orodamaral/drumcore/docs/00-visao-geral.md

# Visão Geral do Projeto

## Objetivo

Desenvolver um módulo MIDI-USB para bateria eletrônica, usando ESP32-S3 como
cérebro do sistema, capaz de:

1. Ler até 32 entradas analógicas (pads piezo simples/aro, pratos 2/3 zonas,
   chimbal simples/2 zonas, pedal de chimbal FSR/óptico) através de 2
   multiplexadores CD4067 (módulo breakout "HW-178", 16 canais cada) — o
   tipo de cada canal é configurável pelo app, ver
   [05-tipos-de-sensor.md](05-tipos-de-sensor.md).
2. Converter os sinais lidos em eventos MIDI (Note On/Off, Control Change) e
   enviá-los via **USB-MIDI nativo** (classe de dispositivo USB, plug-and-play,
   sem necessidade de driver ou software intermediário como Hairless MIDI) e
   também via **BLE-MIDI** (Bluetooth, simultâneo ao USB) — ver
   [01-decisoes-arquiteturais.md](01-decisoes-arquiteturais.md).
3. Prever uma tela (TFT ST7735 1.8" 128x160, SPI, paisagem) e 1 encoder
   rotativo com chave (girar navega/ajusta valor, clicar desce um
   nível/confirma, segurar volta um nível — Fase Y) para configuração do
   módulo diretamente no hardware (sensibilidade, threshold, curva, nota
   MIDI de cada pad, etc).
4. Oferecer um app de configuração, direto pelo navegador (Web Serial), para
   ajustar todos os parâmetros de cada pad, mapeamento de notas e
   backup/restore de configuração.

## Escopo funcional (alto nível)

| # | Funcionalidade | Status |
|---|---|---|
| 1a | Leitura de 32 canais via 2x CD4067/HW-178 (sensing) | Compilado, sem teste em hardware real |
| 1b | Envio MIDI-USB nativo (Note On/Off) | Compilado, sem teste em hardware real |
| 1c | Envio BLE-MIDI simultâneo ao USB (Bluetooth) | Compilado, sem teste em hardware real |
| 2 | Tela TFT (ST7735) + 1 encoder rotativo de configuração (rotate/click/hold, Fase Y) | Compilado, sem teste em hardware real |
| 2b | Persistência EEPROM (config por pad sobrevive a reboot) | Compilado, sem teste em hardware real |
| 2c | Protocolo serial NDJSON (módulo ↔ app) | Compilado, sem teste em hardware real |
| 2d | Nome livre por pad (editável só pelo app) | Compilado/build ok, sem teste em hardware real |
| 2e | 9 tipos de sensor por pad + topologia de canais configurável pelo app | Compilado/build ok, sem teste em hardware real |
| 2f | Navegação de 6 telas (BOOT/LIVE/PADS/PAD_EDIT/SIGNAL/GLOBAL, design/SPEC.md) — substitui a tela/grid da Fase I | Compilado/build ok, sem teste em hardware real |
| 2g | Canal habilitado/desabilitado por pad (evita ruído em slot sem sensor) | Compilado/build ok, sem teste em hardware real |
| 3 | App de configuração (Web Serial, direto pelo navegador), visual unificado com o site | Build/typecheck ok, sem teste com módulo real (só modo demo) |

Projeto renomeado de "HelloDrum" para "DrumCore" em 2026-08-21 (ver
[01-decisoes-arquiteturais.md](01-decisoes-arquiteturais.md), Fase J) — a
biblioteca de terceiros vendorizada mantém o nome original.

## Decisões já tomadas

Ver [01-decisoes-arquiteturais.md](01-decisoes-arquiteturais.md) para o histórico
completo e o racional de cada decisão. Resumo:

- **Placa**: ESP32-S3 (USB OTG nativo → permite USB-MIDI classe de dispositivo).
- **Toolchain**: PlatformIO.
- **Biblioteca base**: [HelloDrum-arduino-Library](https://github.com/RyoKosaka/HelloDrum-arduino-Library),
  vendorizada (fork local) em `firmware/lib/HelloDrum-arduino-Library`, para podermos
  modificar livremente.

## Como este projeto é documentado

- **docs/01-decisoes-arquiteturais.md** — registro de decisões técnicas (estilo ADR),
  com contexto e alternativas consideradas.
- **docs/02-hardware.md** — esquema de ligação (pinout ESP32-S3 ↔ 2x CD4067
  (HW-178) ↔ pads, tela TFT, encoder).
- **docs/03-biblioteca-hellodrum.md** — notas sobre a API da biblioteca base, o que
  foi entendido do código-fonte, e o que foi/será modificado em relação ao original.
- **docs/04-protocolo-serial.md** — contrato de comunicação (NDJSON) entre o
  firmware e o app.
- **docs/05-tipos-de-sensor.md** — os 9 tipos de sensor suportados, quantos
  canais cada um usa, e como o link pedal↔chimbal funciona.
- **docs/06-edicao-arduino.md** — ideia (não implementada) de uma edição para
  Arduino Mega/Uno, incluindo uma versão lite com 16 canais diretos.
- **docs/07-estudo-prato-3-zonas.md** — estudo de como os módulos comerciais
  leem um ride de 3 zonas, e o caminho escolhido (prato de 2 piezos).
- **docs/CHANGELOG.md** — o que foi feito, em ordem cronológica.

Sempre que uma decisão relevante for tomada ou algo novo for aprendido sobre a
biblioteca/hardware, isso deve ser registrado nesses arquivos.
