orodamaral/drumcore/design/DrumCore Logos.dc.html

TURNO 1 · 5 DIREÇÕES

DrumCore — marcas

Marcas tipográficas e geométricas, construídas na mesma paleta da UI. Cada opção mostra a versão grande, a versão 1-bit (para a tela de boot em 128 px) e o ícone quadrado.

1A Pixel · grade de pads

DRUMCORE

DRUMCORE

1-BIT 128PX

ÍCONE

1B Peso partido · sans

DRUMCORE

DRUMCORE

1-BIT 128PX

DC

ÍCONE

1C Núcleo concêntrico · lockup

DRUMCORE

TRIGGER MODULE

DRUMCORE

1-BIT 128PX

ÍCONE

1D Envelope · linha de base

DRUMCORE

DRUMCORE

1-BIT 128PX

ÍCONE

1E Placa · monograma em caixa

DC

DRUMCORE 32 PAD · ESP32-S3

DC

DRUMCORE

1-BIT 128PX

DC

ÍCONE

NA TELA DE BOOT

DRUMCORE

v0.1 ESP32-S3

{{ b.id }} · 128PX @2X
