orodamaral/drumcore/design/Modulo Bateria UI.dc.html

⚠ Desatualizado (Fase Y, 2026-09-04): este mockup ainda mostra a navegação de 2 encoders (ENC1/ENC2). O firmware real usa 1 encoder só (rotate/click/hold) desde a Fase Y — ver design/SPEC.md seção 1-2 pro comportamento atual. Este arquivo não foi reconstruído pro modelo novo.

ESP32-S3 · TFT 1.44" 128x128

Módulo de bateria — UI

Especificação de telas, navegação, tokens e widgets para implementação. Todas as telas são desenhadas em pixels reais de 128x128 e mostradas ampliadas para leitura.

Controles2 rotary encoders c/ botão

Pads32 · grade 8x4

01 — CONTROLES

ENC 1 — página

{{ r.k }} {{ r.v }}

ENC 2 — navegação e valor

{{ r.k }} {{ r.v }}

02 — TELAS

DRUMCORE

32 PAD TRIGGER

v0.1 ESP32-S3

SCR 0 Boot

Exibida durante init de I2S/ADC e leitura da EEPROM. Barra reflete progresso real do boot. Sai automaticamente para LIVE ao terminar; qualquer botão pula a espera.

DRUMCORE

32 PAD TRIGGER

v0.1 ESP32-S3

TAMANHO
REAL

LIVE USBDIN

{{ p.n }}

SCR 1 Live

Tela padrão. Ao receber trigger, o pad acende sólido em laranja por 60 ms e decai em 2 passos (borda laranja, depois idle) em ~180 ms. Nunca redesenhar a grade inteira: só o retângulo do pad.

{{ s.label }}

LIVE USBDIN

{{ p.n }}

TAMANHO
REAL

PADS07/32

{{ r.t }} {{ r.sens }} {{ r.note }}

SCR 2 Lista de pads

8 linhas de 14 px visíveis, janela deslizante sobre os 32 pads. A seleção só rola quando encosta na 1ª ou 8ª linha. Colunas: índice, sensor abreviado, nota MIDI. ENC2 push abre a edição do pad selecionado.

PADS07/32

{{ r.t }} {{ r.sens }} {{ r.note }}

TAMANHO
REAL

PAD 07EDIT

{{ r.k }} {{ r.v }}

ENC2 GIRA VALORPUSH OK

SCR 3 Edição do pad

Os 7 parâmetros cabem sem rolagem (7 × 14 px). Linha selecionada em ciano; ao entrar em modo edição o valor vira caixa âmbar e o giro do ENC2 passa a alterar o número. ENC1 troca de pad sem sair da tela.

{{ p.k }}{{ p.r }}

PAD 07EDIT

{{ r.k }} {{ r.v }}

ENC2 GIRA VALORPUSH OK

TAMANHO
REAL

PAD 07SIGNAL

VEL104PEAK118

SCAN 2MASK 30THR 12

SCR 4 Monitor de sinal

Último envelope capturado do pad (buffer de 120 amostras, 1 px por amostra). Faixa ciano = janela de scan, faixa cinza = mask time, linha âmbar = threshold. Redesenha só quando chega um hit novo, não em loop.

PAD 07SIGNAL

VEL104PEAK118

SCAN 2MASK 30THR 12

TAMANHO
REAL

GLOBAL

{{ r.k }}{{ r.v }}

SALVO 32 PADS EM NVS

SCR 5 Menu global + toast

Ajustes do módulo e ações de persistência. O toast é um overlay de 100×34 px centrado, exibido por 900 ms e depois apagado restaurando a área por baixo. Sem confirmação modal: salvar é ação direta.

GLOBAL

{{ r.k }}{{ r.v }}

SALVO 32 PADS EM NVS

TAMANHO
REAL

03 — MAPA DE NAVEGAÇÃO

BOOT

──▶ init concluído

ENC1 GIRA

{{ p.n }}

◀▶

volta ao início (circular)

ENC2 PUSH

{{ t.from }} {{ t.ev }} ▶ {{ t.to }}

04 — TOKENS

NOME HEX RGB565 USO {{ t.name }} {{ t.hex }} {{ t.r565 }} {{ t.use }}

TIPOGRAFIA

{{ t.k }}{{ t.v }}

MÉTRICA

{{ t.k }}{{ t.v }}

05 — WIDGETS

{{ w.name }} {{ w.size }}

{{ w.desc }}

·{{ r }}
