orodamaral/drumcore/site/assets/schematic.html

DrumCore · Módulo MIDI-USB

# Esquemático de ligação — ESP32-S3

ESP32-S3 ↔ 1 encoder rotativo com chave + tela TFT ST7735 (SPI) de um lado ↔ 2x multiplexador CD4067/HW-178 (32 canais de pad) do outro. Pinout conforme firmware/src/main.cpp (https://github.com/orodamaral/drumcore/blob/master/firmware/src/main.cpp) e docs/02-hardware.md (https://github.com/orodamaral/drumcore/blob/master/docs/02-hardware.md).

Tudo validado em hardware real: encoder + tela (2026-09-06) e as 2 jackboards com MUX (2026-10)

Seleção/leitura dos CD4067/HW-178 (S0–S3, SIG)

SPI — tela TFT ST7735

Encoder rotativo (A/B/SW)

Alimentação (anotada em texto, não desenhada como fio)

Fase Z (2026-09-05): a placa ganhou pads de 3V3/GND extras nos dois headers (modificação física, fora do dev board original) — a divisão deixou de ser "quem precisa de VCC" (Fase L) e passou a ser por função: interface do usuário (encoder + tela, 9 sinais contíguos) no header ESQUERDO; sensing (2x CD4067/HW-178, 6 sinais contíguos) no header DIREITO — mesmo bloco de pinos que os 2 encoders usavam antes das Fases Y/Z. SIG0/SIG1 usam os 2 únicos pinos ADC desse bloco (GPIO2 na jackboard A, GPIO1 na B, ambos ADC1, que funciona com o Wi-Fi ligado); S0-S3 usam os 4 pinos digitais restantes (GPIO39–42). Barramento S0/S1/S2/S3 compartilhado entre os 2 módulos; cada placa usa seu próprio pino SIG. Pontos pretos = junção elétrica real.

### Por que a divisão mudou (Fase Z)

Até a Fase Y, 3V3 só existia no header esquerdo, então o MUX e a tela (que precisam de VCC) ficavam à força ali. A placa física ganhou pads de 3V3/GND extras nos dois headers — isso libera a divisão pra seguir uma lógica de FUNÇÃO em vez de alimentação: encoder + tela (interface) de um lado, MUX (sensing) do outro. Ver docs/01-decisoes-arquiteturais.md (https://github.com/orodamaral/drumcore/blob/master/docs/01-decisoes-arquiteturais.md) (Fase Z).

### MUX: ADC1 em vez de ADC2

O bloco contíguo do header direito (1,2,42,41,40,39) só tem 2 pinos com ADC: GPIO1/GPIO2 (ADC1_CH0/CH1) — por isso SIG0/SIG1 ficam neles, e S0-S3 (sem precisar de ADC) ficam nos outros 4. Antes (Fase L) o MUX usava ADC2 (GPIO15/16), que exigia justificar que não haveria conflito com Wi-Fi. Em ADC1 esse cuidado nem precisa existir.

### Tela: espelhada com o conector de novo (2026-09-06)

Na Fase Z, a tela passou a seguir só a contiguidade com o encoder, sem se preocupar em casar com a ordem do conector dela. A pedido do Rodrigo, isso mudou de novo: dentro do bloco fixo 7,15,16,17,18,8 (a posição do bloco não mudou), os 6 sinais foram reordenados pra bater com a sequência física do conector da tela (GND VDD SCL SDA RES DC CS BLK) — SCL(7) → SDA(15) → RES(16) → DC(17) → CS(18) → BLK(8). GND/VDD da tela vão em pads extras perto desse bloco (não existe 3V3/GND de fábrica bem ali).

### Pinos evitados

- Strapping pins (GPIO0, 3, 45, 46)
- Pinos do USB nativo (GPIO19/20 — usados pelo USB-MIDI)
- GPIO38 — aciona um LED embutido (BUILTIN LED) dessa placa específica
- GPIO47/48 — internos de flash/PSRAM nessa placa; GPIO48 também é o LED RGB endereçável (RGB LED)
- GPIO43/44 — não estão livres: são o UART físico usado pelo Serial (protocolo NDJSON)

### HW-178 (CD4067) — pino EN fixo em GND

O breakout expõe um pino EN (enable, ativo em LOW) que a lib não controla — decisão de fiação, não de firmware: ligado direto em GND nas 2 placas, sempre habilitadas. Como cada MUX tem seu próprio pino SIG, não há necessidade de desabilitar um deles em nenhum momento.

### Encoder — sem resistor externo

A/B/SW usam INPUT_PULLUP interno do ESP32-S3 (ver firmware/src/main.cpp (https://github.com/orodamaral/drumcore/blob/master/firmware/src/main.cpp)) — não precisa de resistor de pull-up na placa. O módulo físico que chegou também tem pull-ups próprios (VCC no 3V3) — os dois ativos ao mesmo tempo não causam problema elétrico.

### Histórico de ajustes de pinout

2026-08-31: contiguidade dentro de cada header. Fase Y (2026-09-04): 2 encoders → 1 só, o que sobrou ficou em GPIO41/40/39 (GPIO1/2/42 livres). Fase Z (2026-09-05): encoder + tela migraram pro header esquerdo (mesmo bloco contíguo 4,5,6,7,15,16,17,18,8); o MUX migrou pro header direito (bloco 1,2,42,41,40,39, o mesmo que os 2 encoders usavam antes). 2026-10-01: ajustado na montagem da jackboard A — S0–S3 = GPIO39/40/41/42 (ordem invertida) e os SIGs trocaram (A = GPIO2, B = GPIO1).

### O que já foi validado, o que ainda não

Validado (2026-09-06): encoder (GPIO4/5/6, navegação girar/clicar/segurar confirmada) e tela (GPIO7/15/16/17/18/8, imagem confirmada). Validado (2026-10): as 2 jackboards montadas com os CD4067 — os 32 canais lidos pelo MUX, com pads de piezo, caixa 3 zonas e o controlador de chimbal (sensor Hall SS49E) no jack 1.

## Referência de pinout

Encoder rotativo — header esquerdo

Sinal | GPIO
A | 4
B | 5
SW (click/hold) | 6

Tela TFT ST7735 — header esquerdo

Sinal | GPIO
SCL (SCK) | 7
SDA (MOSI) | 15
RES | 16
DC | 17
CS | 18
BLK | 8

2x CD4067/HW-178 (32 canais) — header direito

Sinal | GPIO
S0 (compartilhado) | 39
S1 (compartilhado) | 40
S2 (compartilhado) | 41
S3 (compartilhado) | 42
SIG — jackboard A (pads 0–15) | 2
SIG — jackboard B (pads 16–31) | 1

Projeto DrumCore — módulo MIDI-USB para bateria eletrônica. Ver docs/02-hardware.md (https://github.com/orodamaral/drumcore/blob/master/docs/02-hardware.md), docs/01-decisoes-arquiteturais.md (https://github.com/orodamaral/drumcore/blob/master/docs/01-decisoes-arquiteturais.md) e docs/05-tipos-de-sensor.md (https://github.com/orodamaral/drumcore/blob/master/docs/05-tipos-de-sensor.md) no repositório para o racional completo de cada decisão. Licenciado sob CC BY-NC 4.0 (https://github.com/orodamaral/drumcore/blob/master/LICENSE) — uso e cópia livres, sem fins comerciais, sempre citando a fonte.
