orodamaral/drumcore/docs/04-protocolo-serial.md

# Protocolo Serial (módulo ↔ app)

Contrato de comunicação entre o firmware (ESP32-S3, via USB-CDC — a mesma
porta serial já usada pra debug desde a Fase B) e o app de configuração.

## Formato

**NDJSON** (um objeto JSON por linha, terminado em `\n`). Todo o tráfego
Serial usa esse formato — inclusive os eventos de "pad atingido", que antes
eram texto livre (`Serial.print`) e passaram a ser JSON também, pra manter o
stream inteiro consistente e fácil de parsear do lado do app (sem precisar
filtrar linhas de debug misturadas com linhas de protocolo).

Baud rate: 115200 (definido em `firmware/platformio.ini`).

## Canais "primary" vs. canais consumidos

Desde a Fase G (tipos de sensor — ver
[05-tipos-de-sensor.md](05-tipos-de-sensor.md)), nem todo canal (0-31) é um
pad independente: tipos de 2 canais (aro, prato 2/3 zonas, chimbal 2 zonas)
consomem o canal seguinte. Um `pad_config` sempre tem um campo `primary`:

- `"primary": true` — pad independente, com todos os campos de configuração
  (ver tabela abaixo).
- `"primary": false` — canal consumido pelo pad anterior; só tem `pad` e
  `consumed_by` (índice do pad que o está usando). Não aceita `set_pad`
  (retorna `error` com `channel_consumed`).

## Comandos (app → módulo)

Cada linha enviada pelo app é um objeto com um campo `cmd`.

| `cmd` | Campos extras | Descrição |
|---|---|---|
| `ping` | — | Testa a conexão. Resposta: `pong`. |
| `get_device_info` | — | Informações gerais do módulo. Resposta: `device_info`. |
| `get_pad` | `pad` (0-31) | Configuração de um pad. Resposta: `pad_config`. |
| `get_all_pads` | — | Configuração de todos os 32 pads (32 respostas `pad_config` em sequência). |
| `set_pad` | `pad` (0-31), `field`, `value` | Altera um parâmetro de um pad, aplica imediatamente e persiste em EEPROM. Resposta varia por campo (ver tabela) ou `error`. |
| `set_global` | `field`, `value` | Altera uma configuração global (ver tabela abaixo), aplica imediatamente e persiste em EEPROM. Resposta: `ack` + `device_info`. |
| `save_all` | — | Grava toda a configuração atual (32 pads + globais) na EEPROM. Resposta: `log` + `device_info`. Esse comando existe principalmente pro caminho dos encoders/tela (Fase J — ver [01-decisoes-arquiteturais.md](01-decisoes-arquiteturais.md)), onde a edição só fica em RAM até `GLOBAL > SALVAR`; pelo protocolo serial ele é redundante na prática, já que `set_pad`/`set_global` já persistem a cada mudança. |
| `restore_all` | — | Descarta qualquer mudança em RAM e recarrega os 32 pads + globais da EEPROM. Resposta: `pad_config` × 32 + `log` + `device_info`. |
| `factory_reset` | `confirm` (`true`, obrigatório) | Apaga a configuração atual e grava o mapeamento de fábrica (ver [02-hardware.md](02-hardware.md), "Mapeamento de fábrica") em RAM e EEPROM. Sem `"confirm": true` responde `error` `confirm_required`. Resposta: `pad_config` × 32 + `jack_config` × 16 + `log` + `device_info`. |
| `get_timing` | — | Diagnóstico: responde um `log` com o tempo médio e máximo de uma volta do loop (= intervalo entre 2 leituras do mesmo canal) na última janela de 1 s, e quantos canais estão em uso. |
| `set_wifi` | `enabled` e/ou `autostart` (`true`/`false`) | Liga/desliga o Wi-Fi do módulo (ConfigTool servido pela placa, ver [08-wifi.md](08-wifi.md)); `autostart` = ligar sozinho quando o módulo liga (persistido, padrão desligado). Sem nenhum dos dois: `error` `invalid_value`. Resposta: `log` + `device_info` (com `wifi`). Firmware anterior a 2026-10-03 responde `error` `unknown_cmd`. |
| `set_wifi_network` | `ssid` (1-32 caracteres), `password` (vazio = rede aberta, ou 8-63) | Salva a rede de casa (a senha fica só na placa, nunca volta no `device_info`). Com o Wi-Fi ligado, já tenta conectar — a rede própria continua no ar enquanto isso e desliga 30 s depois de conectar. `error` `invalid_value` fora das faixas. Resposta: `log` + `device_info`. |
| `retry_wifi_network` | — | Tenta de novo a rede de casa salva (depois de `sta_state` `failed`). `error` `not_ready` se o Wi-Fi estiver desligado ou não houver rede salva. Resposta: `device_info`. |
| `forget_wifi_network` | — | Apaga a rede de casa. Com o Wi-Fi ligado, volta pra rede própria. Resposta: `log` + `device_info`. |
| `ota_request` | — | Pede pra atualizar o firmware pelo Wi-Fi ([08-wifi.md](08-wifi.md), fase 3): a tela do módulo pergunta e só um **clique no encoder** libera o envio (`POST /update`) por 2 min. Sem clique em 1 min, expira. `error` `wifi_off` (Wi-Fi desligado) ou `busy` (gravação em andamento). Resposta: `ota_status` (`confirm`). |
| `ota_cancel` | — | Cancela um pedido de atualização (não interrompe uma gravação em andamento). Resposta: `ota_status`. |
| `scan_wifi` | — | Procura redes Wi-Fi próximas (só com o Wi-Fi ligado — `error` `wifi_off` caso contrário). Resposta, alguns segundos depois: `wifi_scan`. |
| `get_jacks` | — | Apelidos dos 16 jacks (tela LIVE). Resposta: `jack_config` × 16. Firmware anterior a 2026-09-27 responde `error` `unknown_cmd`. |
| `set_jack` | `jack` (0-15), `field` (`"label"`), `value` (string) | Apelido do jack na tela LIVE: até **6** caracteres ASCII imprimíveis (vazio = a tela mostra o nome do pad do tip, ou do ring). Persiste em EEPROM. `error` `invalid_jack` / `invalid_label` / `unknown_field` caso contrário. Resposta: `jack_config`. |
| `start_autotune` | `pad` (0-31) | Inicia o assistente de auto-calibração (Fase O) pra esse pad — ver [01-decisoes-arquiteturais.md](01-decisoes-arquiteturais.md). `error` (`invalid_pad`) se o pad não existir/não for `primary`, (`channel_disabled`) se o canal estiver desligado (`enabled: false`, Fase N), ou (`not_applicable_for_choke`) se `pad_type` for 9 (`PAD_CHOKE` — gatilho binário, sem envelope de piezo pra calibrar). Resposta: uma série de `autotune_status` conforme o assistente avança (não é só uma resposta única — ver abaixo). |
| `cancel_autotune` | — | Cancela o assistente em qualquer fase (mesmo no meio da coleta de golpes). Resposta: `autotune_status` com `"state": "idle"`. |
| `apply_autotune` | — | Aplica o resultado calculado (`sensitivity`/`threshold`/`scan_time`/`mask_time`, mais `rim_sensitivity`/`rim_threshold` em pads de 2+ zonas e `curve_type`/`retrigger` em pads de impacto) no pad, **força `gain` = 100** (o resultado é medido com gain neutro) e persiste tudo em EEPROM na hora — também quando o apply é feito pela tela física (até 2026-09-26 só ficava em RAM até o SALVAR). Só funciona depois de um `autotune_status` com `"state": "done"` — `error` (`not_ready`) caso contrário. Resposta: `autotune_status` (`idle`) + `pad_config` com os novos valores. |
| `enc_input` | `enc` (1 ou 2), `action` (`rotate`\|`click`\|`hold`), `delta` (só em `rotate`, padrão `1`) | Encoder virtual — Fase Q, criado pra navegar/testar a tela do módulo pelo app antes dos encoders físicos estarem conectados. Chama exatamente o mesmo handler do encoder físico único (`onEncRotate`/`onEncClick`/`onEncHold`, ver `firmware/src/main.cpp`), então tem efeito idêntico ao giro/clique/hold real. **Fase Y (2026-09-04)**: o hardware passou a ter 1 encoder só, mas `enc` continua aceitando `1` ou `2` por compatibilidade com o app existente — os dois valores caem no mesmo handler. Sem resposta dedicada — o resultado aparece na tela física do módulo, que é a única fonte da verdade de navegação (o app não espelha `currentPage`/item selecionado/etc). `error` (`invalid_enc`, `invalid_action` ou `invalid_delta`) em caso de parâmetro inválido. |

`field` aceito em `set_global`:

| `field` | Tipo de `value` | Faixa/limite |
|---|---|---|
| `midi_channel` | número | `1-16` |
| `midi_output` | número | `0` USB, `1` BLE, `2` USB+BLE — sem MIDI DIN, o hardware não tem esse circuito (ver [01-decisoes-arquiteturais.md](01-decisoes-arquiteturais.md)) |

`field` aceito em `set_pad` (nomes do protocolo, não os nomes internos da
lib — ver [05-tipos-de-sensor.md](05-tipos-de-sensor.md) pro que cada campo
significa em cada tipo de pad):

| `field` | Tipo de `value` | Faixa/limite | Resposta em caso de sucesso |
|---|---|---|---|
| `sensitivity` | número | `0-100` | `ack` |
| `threshold` | número | `0-100` | `ack` |
| `scan_time` | número | `0-100` | `ack` |
| `mask_time` | número | `0-100` | `ack` |
| `curve_type` | número | `0-4` | `ack` |
| `retrigger` | número | `0-100` (Fase P) | `ack` |
| `gain` | número | `10-200` (0.10x-2.00x, 100 = neutro) (Fase P) | `ack` |
| `xtalk` | número | `0-100` (Fase P) | `ack` |
| `xtalk_group` | número | `0-4` (`0` = nenhum grupo) (Fase P) | `ack` |
| `rim_sensitivity` | número | `0-100` | `ack` |
| `rim_threshold` | número | `0-100` | `ack` |
| `note` | número | `0-127` | `ack` |
| `note_rim` | número | `0-127` | `ack` |
| `note_cup` | número | `0-127` | `ack` |
| `label` | string | até 19 caracteres | `pad_config` |
| `pad_type` | número | `0-8` (ver tabela em [05-tipos-de-sensor.md](05-tipos-de-sensor.md)); tipos de 2 canais só num pad cujo canal 0-based é par (**tip** do jack) e nunca no último pad — `error` `two_channel_needs_tip` / `no_second_channel` caso contrário | `pad_config` do próprio pad **e** do pad seguinte (pode ter mudado de status) |
| `hihat_pedal_channel` | número | índice de outro pad (`6`/`7`), ou `-1` pra remover o link | `pad_config` |
| `enabled` | número | `0` ou `1` | `pad_config` |
| `hihat_invert` | número | `0` ou `1` (só pad_type `6`/`7`, Fase X) | `pad_config` |
| `pedal_note` | número | `0` ou `1` (só pad_type `6`/`7`): `0` = não manda a nota de chick ao fechar, só o CC de posição (2026-09-27) | `pad_config` |
| `pedal_cc` | número | `0-127` (só pad_type `6`/`7`): número do CC de posição do pedal, padrão `4` (2026-09-27) | `ack` |

Todos os campos exigem que o pad seja `primary` (`error` com
`channel_consumed` caso contrário). `pad_type`/`hihat_pedal_channel`/
`enabled`/`hihat_invert`/`pedal_note` e `label` respondem com o `pad_config` inteiro
(mais direto o app já receber o estado recalculado) em vez de `ack`.

`retrigger`/`gain`/`xtalk`/`xtalk_group` (Fase P, ver
[01-decisoes-arquiteturais.md](01-decisoes-arquiteturais.md), inspirados no
microDRUM/nanoDRUM): `retrigger` afrouxa o `mask_time` pra pancadas bem mais
fortes que a anterior (rufos/rolls rápidos); `gain` recalibra a amplitude
lida do sensor antes do threshold (útil pra piezos com saída muito
forte/fraca); `xtalk`/`xtalk_group` suprimem um hit se outro pad do mesmo
grupo bateu bem mais forte no mesmo instante (vibração mecânica entre pads
montados juntos, ou crosstalk elétrico entre canais — inclusive os dois
CD4067 que compartilham o barramento S0-S3, ver
[02-hardware.md](02-hardware.md)). Nenhum dos 4 tem efeito quando no valor
neutro (`0` pros 3 primeiros, `100` pro `gain`).

`enabled` (Fase N, ver
[01-decisoes-arquiteturais.md](01-decisoes-arquiteturais.md)): `false`
desliga o canal por completo — o firmware não roda sensing nem emite `hit`
pra ele, mesmo que o pino ADC correspondente esteja fisicamente flutuando
(sem sensor conectado) e captando ruído. Não afeta `primary`/
`consumed_by`, que continuam decididos só por `pad_type` — um canal
desabilitado ainda "existe" no espaço de 32 canais, só não é sensoreado.

`hihat_invert` (Fase X, controlador de pedal — `pad_type` `6`/`7` — ver
[01-decisoes-arquiteturais.md](01-decisoes-arquiteturais.md)): alguns
sensores de posição mandam o sinal invertido (pedal fechado = CC baixo,
quando deveria ser alto, ou vice-versa). `true` inverte o CC final
(`127 - pedalCC`) — efeito imediato, não precisa recalibrar depois de
mudar (não mexe em `threshold`/`sensitivity`, só no valor que sai no MIDI
CC). Ignorado nos outros tipos de pad.

## Eventos/respostas (módulo → app)

Cada linha enviada pelo módulo é um objeto com um campo `type`.

| `type` | Campos | Quando é enviado |
|---|---|---|
| `pong` | — | Resposta a `ping`. |
| `device_info` | `pads`, `muxes`, `midi_channel`, `midi_output`, `ble_connected`, `firmware_phase`, `firmware_version`, `wifi` | Resposta a `get_device_info`, `set_global`, `set_wifi`, `save_all` e `restore_all`. `wifi` (desde 2026-10-03): `active`, `ap_active` (rede própria no ar), `ssid`/`password` (rede própria), `hostname` (`"drumcore"` → `drumcore.local`), `ip` (na rede própria; vazio se ela não estiver no ar), `sta_ssid` (rede de casa salva, `""` = nenhuma), `sta_state` (`none`/`connecting`/`connected`/`failed`), `sta_ip`, `ap_off_in_ms` (quanto falta pra rede própria desligar depois de conectar na de casa; `0` = não vai desligar), `autostart`, `ota` (`true` = aceita atualização pelo Wi-Fi) e `clients` (apps conectados pelo WebSocket) — ver [08-wifi.md](08-wifi.md). Também é enviado sozinho quando a rede de casa conecta/cai ou a rede própria liga/desliga. `ble_connected` indica se há um dispositivo pareado via BLE-MIDI naquele momento (ver [01-decisoes-arquiteturais.md](01-decisoes-arquiteturais.md)). `midi_output` controla se o MIDI sai por USB, BLE ou os dois — antes (Fase H) saía sempre pelos dois simultaneamente; agora é configurável via `set_global`. |
| `pad_config` | Ver abaixo | Resposta a `get_pad`/`get_all_pads`, e a `set_pad` bem-sucedido em `label`/`pad_type`/`hihat_pedal_channel`/`enabled`/`hihat_invert`/`pedal_note`, e a `apply_autotune`. |
| `hit` | `pad`, `zone`, `note`, `velocity` | Sempre que um pad é atingido (telemetria em tempo real). `zone` varia por tipo: `"bow"`, `"head"`, `"rim"`, `"edge"`, `"cup"`, `"open"`, `"closed"`, `"pedal"`, `"choke"` (abafamento de prato/aro, `pad_type` 3/5) ou `"touch"` (`pad_type` 9 — `PAD_CHOKE`, sensor de contato; `velocity` sempre `127`) — ver [05-tipos-de-sensor.md](05-tipos-de-sensor.md). |
| `ack` | `cmd`, `pad`, `field`, `value` | Confirmação de um `set_pad` com campo numérico simples. |
| `autotune_status` | `pad`, `state`, `hit_count`, e (`state == "collecting"`) `tier`/`tier_index`/`tier_count`/`tier_elapsed_ms`/`tier_target_ms`/`zone`? **ou** `phase`/`hold_elapsed_ms`/`hold_target_ms` (pedal, ver abaixo), e (`state == "done"`) `sensitivity`/`threshold`/`scan_time`/`mask_time`/`rim_sensitivity`?/`rim_threshold`?/`curve_type`?/`retrigger`?/`mode`?, ou (`state == "aborted"`) `reason` | Progresso do assistente de auto-calibração (Fase O, 3 níveis de força desde a Fase T, 2ª/3ª zona pra pads de mais de 1 canal desde a Fase U/V, fluxo de posição contínua pro controlador de pedal desde a Fase X, coleta por janela de tempo desde a Fase AA, `curve_type`/`retrigger` inferidos desde a Fase AB) — emitido a cada mudança de fase relevante, não só em resposta a comando (dá pra acompanhar em tempo real: contagem regressiva do ruído, janela de tempo do nível, golpes capturados, etc). `state`: `"idle"` (parado/cancelado/aplicado), `"noise"` (medindo ruído de fundo — não acontece pro pedal, ver abaixo), `"collecting"` (esperando/processando golpes, ou segurando o pedal numa posição), `"done"` (resultado calculado, esperando `apply_autotune`/`cancel_autotune`), `"aborted"` (timeout de 15s sem pancada, ou canal desligado — ver `reason`: `"timeout"` ou `"channel_disabled"`). Em `"collecting"`, `tier` indica qual nível está em coleta agora — `"weak"`, `"medium"` ou `"strong"` — e `tier_index`/`tier_count` (ex: `2`/`3`) dão o progresso entre níveis; `tier_elapsed_ms`/`tier_target_ms` dão o progresso *dentro* do nível atual (mesmo padrão do `hold_elapsed_ms`/`hold_target_ms` do pedal, ver abaixo). `hit_count` conta as batidas capturadas *na zona/nível atual* (só informativo — não é mais alvo de nada). Cada zona pede 10s de golpes fracos, depois 10s de médios, depois 10s de fortes ([Fase AA](01-decisoes-arquiteturais.md), substitui a meta fixa de 8 golpes por nível usada até então — mais amostras por nível, média mais confiável) — ver [01-decisoes-arquiteturais.md](01-decisoes-arquiteturais.md). `zone` só aparece quando o pad calibrado tem mais de 1 canal, e reaproveita o MESMO vocabulário do evento `hit` (não é um nome genérico): `"head"`/`"rim"` pra `pad_type` 1 (`PAD_DUAL`, 1 rodada extra); `"bow"`/`"edge"`/`"cup"` pra `pad_type` 5 (`PAD_CYMBAL_3ZONE`, 2 rodadas extras); `"head"`/`"edge"`/`"rim"` pra `pad_type` 8 (`PAD_SNARE_3ZONE`, 2 rodadas extras) — a 1ª zona de cada lista já aparece na 1ª rodada (não só nas extras). O resultado final em `"done"` ganha `rim_sensitivity`/`rim_threshold` também nesses casos (mesmos campos do `pad_config`, reaproveitados com significado diferente por `pad_type` — ver tabela de campos por tipo em [05-tipos-de-sensor.md](05-tipos-de-sensor.md)). `curve_type` (0-4, mesma escala do campo `CURVA` do `pad_config`) e `retrigger` (0-100, mesma escala do campo `RETRIG`) vêm inferidos automaticamente a partir da própria coleta ([Fase AB](01-decisoes-arquiteturais.md)) — presentes em todo resultado de pad de impacto, ausentes quando `mode === "hihat_range"` (não fazem sentido pro pedal). **Controlador de pedal** (`pad_type` 6/7, Fase X, fora das mudanças da Fase AA/AB): fluxo totalmente diferente — sensor de posição contínua, sem "golpes"/níveis. Pula direto pra `"collecting"` com `phase` (`"hh_open"` = segure o pedal solto, `"hh_closed"` = pressione até o fim) e `hold_elapsed_ms`/`hold_target_ms` (progresso dentro dos 10 s de cada posição — eram 3 s até 2026-10-02 — `tier`/`tier_elapsed_ms`/`tier_target_ms`/`zone` não se aplicam). O resultado em `"done"` ganha `mode: "hihat_range"`, avisando que `sensitivity`/`threshold` são o teto/piso de posição (pedal fechado/aberto), não pico de pancada — e não ganha `curve_type`/`retrigger`. |
| `error` | `cmd`, `message` | Comando inválido, campo desconhecido, valor fora da faixa, canal consumido, JSON malformado, etc. |
| `ota_status` | `state` (`idle`/`confirm`/`armed`/`receiving`/`done`/`error`), `percent`, `error`? | Andamento da atualização pelo Wi-Fi — enviado a cada mudança de estado e a cada 5% gravados. `error`: `invalid_image`, `wrong_chip`, `too_big`, `write_failed`, `verify_failed`, `upload_stalled`. Em `done`, o módulo reinicia ~1,5 s depois, já com o Wi-Fi ligado. |
| `wifi_scan` | `networks` (`[{ssid, rssi, secure}]`, sem repetir nome, a mais forte primeiro, até 15), `error`? (`scan_failed`) | Resultado de `scan_wifi`. |
| `jack_config` | `jack`, `label` | Apelido de um jack (resposta a `get_jacks`/`set_jack`, e também enviado após `factory_reset`/`restore_all`). `jack` é o índice 0-based (jack 1 = canais 0 e 1). |
| `log` | `message` | Mensagens informativas de boot/diagnóstico (antes eram `Serial.println` livres), e também pareamento/desconexão do BLE-MIDI. |

### `pad_config` — canal consumido (`primary: false`)

```json
{"type":"pad_config","pad":4,"primary":false,"consumed_by":3}
```

### `pad_config` — pad independente (`primary: true`)

```json
{
  "type": "pad_config",
  "pad": 3,
  "primary": true,
  "pad_type": 0,
  "uses_second_channel": false,
  "name": "4 - Caixa",
  "label": "Caixa",
  "sensitivity": 100,
  "threshold": 10,
  "scan_time": 10,
  "mask_time": 30,
  "curve_type": 0,
  "retrigger": 0,
  "gain": 100,
  "xtalk": 0,
  "xtalk_group": 0,
  "rim_sensitivity": 20,
  "rim_threshold": 3,
  "note": 39,
  "note_rim": 39,
  "note_cup": 40,
  "hihat_pedal_channel": -1,
  "enabled": true,
  "hihat_invert": false,
  "pedal_note": true,
  "pedal_cc": 4
}
```

`name` é o nome pronto pra exibir (`"N - label"` ou `"Pad N"` sem label);
`label` é o texto livre "crú", útil pra preencher um campo de edição sem o
prefixo do número (ver [01-decisoes-arquiteturais.md](01-decisoes-arquiteturais.md)).

## Exemplos

Alterar a sensibilidade do pad 3:
```json
{"cmd":"set_pad","pad":3,"field":"sensitivity","value":80}
```
Resposta:
```json
{"type":"ack","cmd":"set_pad","pad":3,"field":"sensitivity","value":80}
```

Renomear o pad 3 (índice 0-based → exibido como pad 4):
```json
{"cmd":"set_pad","pad":3,"field":"label","value":"Caixa"}
```

Transformar o pad 5 num prato de 2 zonas (consome também o pad 6):
```json
{"cmd":"set_pad","pad":5,"field":"pad_type","value":3}
```
Respostas (2 linhas — o próprio pad e o seguinte, que passa a `primary:false`):
```json
{"type":"pad_config","pad":5,"primary":true,"pad_type":3, ...}
{"type":"pad_config","pad":6,"primary":false,"consumed_by":5}
```

Linkar o chimbal (pad 10, tipo 2 ou 4) ao pedal (pad 12, tipo 6 ou 7):
```json
{"cmd":"set_pad","pad":10,"field":"hihat_pedal_channel","value":12}
```

Girar o encoder um passo pra frente (ex: navegar a lista de pads):
```json
{"cmd":"enc_input","enc":1,"action":"rotate","delta":1}
```
Clicar o encoder (ex: entrar na linha "SINAL" de PAD_EDIT pra abrir a tela SIGNAL):
```json
{"cmd":"enc_input","enc":1,"action":"click"}
```

Evento de hit num prato 3 zonas (zona "cup"):
```json
{"type":"hit","pad":5,"zone":"cup","note":40,"velocity":112}
```

Progresso do auto-tune no meio do nível médio (6.2s dos 10s da janela, 5 golpes capturados até agora):
```json
{"type":"autotune_status","pad":3,"state":"collecting","tier":"medium","tier_index":2,"tier_count":3,"tier_elapsed_ms":6200,"tier_target_ms":10000,"hit_count":5}
```

Auto-tune de um pad `PAD_DUAL` (`pad_type` 1) na rodada extra do aro, nível fraco (2.1s dos 10s, 2º golpe):
```json
{"type":"autotune_status","pad":0,"state":"collecting","tier":"weak","tier_index":1,"tier_count":3,"zone":"rim","tier_elapsed_ms":2100,"tier_target_ms":10000,"hit_count":2}
```
Resultado final desse mesmo pad (`rim_sensitivity`/`rim_threshold` só aparecem pra pads de mais de 1 canal; `curve_type`/`retrigger` inferidos automaticamente, Fase AB):
```json
{"type":"autotune_status","pad":0,"state":"done","hit_count":11,"sensitivity":72,"threshold":8,"scan_time":12,"mask_time":38,"rim_sensitivity":45,"rim_threshold":6,"curve_type":3,"retrigger":22}
```

Auto-tune de um prato 3 zonas (`pad_type` 5) na rodada extra do cup, nível forte (9.1s dos 10s) — note que já foram 2 rodadas extras antes dessa (`edge`, depois `cup`):
```json
{"type":"autotune_status","pad":7,"state":"collecting","tier":"strong","tier_index":3,"tier_count":3,"zone":"cup","tier_elapsed_ms":9100,"tier_target_ms":10000,"hit_count":13}
```

Auto-tune de um controlador de pedal (`pad_type` 6/7) segurando a posição fechada, 1.4s dos 3s (fluxo HHC, fora da mudança da Fase AA — continua por contagem de tempo fixa, não por golpes):
```json
{"type":"autotune_status","pad":12,"state":"collecting","phase":"hh_closed","hold_elapsed_ms":1400,"hold_target_ms":10000,"hit_count":0}
```
Resultado final desse mesmo pedal (`mode: "hihat_range"` avisa que `sensitivity`/`threshold` são o teto/piso de posição, não pico de pancada):
```json
{"type":"autotune_status","pad":12,"state":"done","hit_count":0,"sensitivity":92,"threshold":8,"scan_time":10,"mask_time":30,"mode":"hihat_range"}
```

Invertendo o CC de um controlador de pedal (`pad_type` 6/7):
```json
{"cmd":"set_pad","pad":12,"field":"hihat_invert","value":1}
```

## Implementação

- **Firmware**: `firmware/src/main.cpp`, usando a lib `ArduinoJson`
  (`bblanchon/ArduinoJson`) pra serializar/parsear. Leitura de linha não-
  bloqueante (acumula caracteres até `\n`, sem travar o `loop()` — não
  podíamos usar algo como `Serial.readStringUntil()` com timeout, que
  pausaria o sensing/MIDI).
- **App**: `web-app/`, direto pelo navegador via **Web Serial API**
  (`navigator.serial`) — sem processo nativo/instalação, roda como página web.
- **Wi-Fi** (desde 2026-10-03, ver [08-wifi.md](08-wifi.md)): o mesmo
  protocolo passa por um **WebSocket** em `ws://<placa>/ws` — 1 comando por
  mensagem; cada linha que o módulo manda pela serial vai também, igual, pra
  todos os clientes do WebSocket. Os comandos que chegam pelo Wi-Fi entram
  numa fila e são executados no `loop()` principal, pelo mesmo
  `handleSerialCommand()`.

## Em aberto / não coberto ainda

- Sem SysEx/MIDI — a config é só via essa porta serial, não pelo cabo MIDI.
- Sem comando de "reset pad pros defaults" (só dá pra fazer isso apagando a
  flag de EEPROM, o que reseta *todos* os pads).
- Sem autenticação/validação de origem — qualquer software que abra a porta
  serial correta pode configurar o módulo. Aceitável pra um dispositivo
  local via USB. Pelo Wi-Fi, a proteção é a senha da rede própria do módulo
  (ver [08-wifi.md](08-wifi.md)).
- Nada disso foi testado com hardware real ainda (ver
  [05-tipos-de-sensor.md](05-tipos-de-sensor.md), seção final).

## Arquivo de configuração do ConfigTool (backup / compartilhamento)

Não é um comando do protocolo: o ConfigTool (aba Global > "Backup e
compartilhamento") exporta um JSON a partir dos `pad_config` que já tem e,
ao importar, transforma o arquivo numa fila de `set_pad`/`set_global` — só
o que muda, um comando por vez esperando a resposta (`ack` ou `pad_config`).
Implementação em `web-app/src/configFile.ts`.

```json
{
  "format": "drumcore-config",
  "version": 1,
  "exported_at": "2026-09-27T19:00:00.000Z",
  "firmware_version": "fw-v0.0.7-test",
  "pad_count": 32,
  "global": { "midi_channel": 10, "midi_output": 2 },
  "app": { "midi_map": "ad2" },
  "pads": [
    {
      "pad": 6, "pad_type": 8, "label": "Snare", "enabled": true,
      "hihat_pedal_channel": -1, "hihat_invert": false, "pedal_note": true,
      "sensitivity": 100, "threshold": 10, "scan_time": 10, "mask_time": 30,
      "curve_type": 0, "retrigger": 0, "gain": 100, "xtalk": 0, "xtalk_group": 0,
      "rim_sensitivity": 20, "rim_threshold": 3,
      "note": 38, "note_rim": 43, "note_cup": 37, "pedal_cc": 4
    }
  ]
}
```

- `jacks` (opcional): `[{ "jack": 3, "label": "Snare" }, ...]` — apelidos da
  tela LIVE. Importados junto com os nomes dos pads.
- `pads` lista só os pads **primários** (o 2º canal de um pad de 2 zonas não
  tem configuração própria); `pad` é o índice 0-based, igual ao protocolo.
  Campos e faixas iguais aos de `set_pad` acima.
- Ordem de aplicação no import: (1) `pad_type`, do pad 0 ao 31 — subindo em
  ordem, cada pad já é primário quando chega a vez dele; (2) `label`,
  `enabled`, `hihat_invert` e campos numéricos do tipo; (3)
  `hihat_pedal_channel` (o alvo precisa já ser pedal); (4) `set_global`.
- Validação antes de aplicar: `format`/`version`, faixas de cada campo, a
  regra do tip (2 zonas só em pad de canal par) e links de pedal. O que não
  passa vira aviso no diálogo e é ignorado; o resto é importado.
- `version` só sobe em mudança incompatível; campos desconhecidos são
  ignorados.
