orodamaral/drumcore/Tela2-1.jpeg

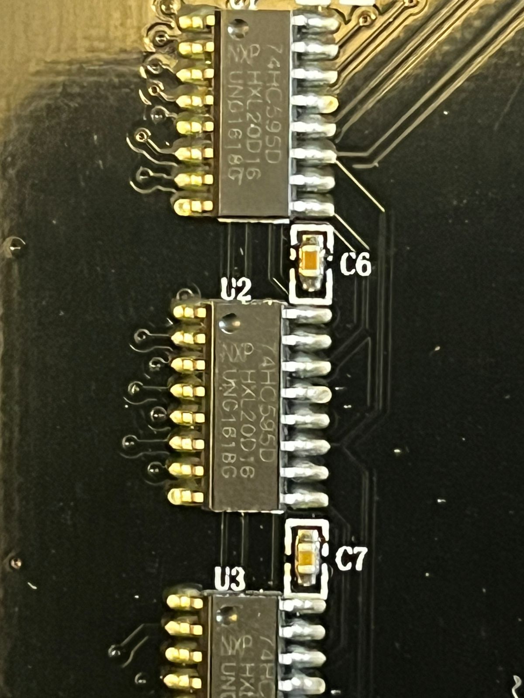
Tela2-1.jpeg
